Dsate11/Paladarium/images/panel_base.jpg

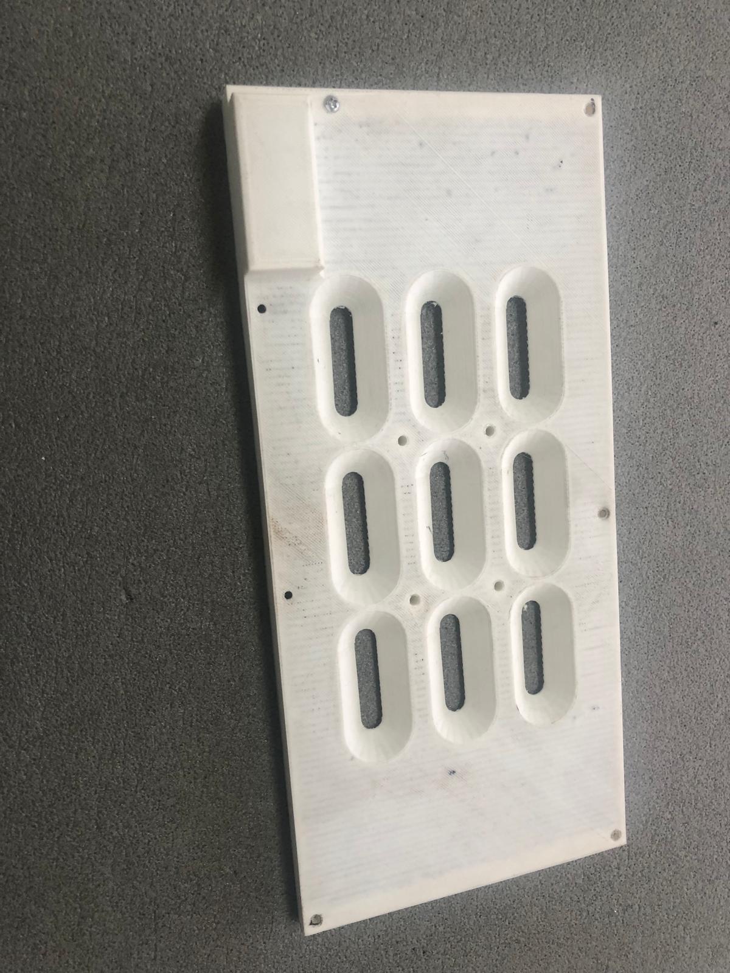
images/panel_base.jpg
