Dsate11/Paladarium/ecosistema_paladario/src/dht11.h

#ifndef DHT11_H
#define DHT11_H

#include "esp_err.h"
#include "driver/gpio.h"

esp_err_t dht11_read(gpio_num_t pin, float *humidity, float *temperature);

#endif // DHT11_H
#pragma once
// DHT header removed. Intentionally empty to remove sensor support.
